jchen208208/SPARC-Spotify-Proximity-and-Remote-Control/core.py

# serial/Bluetooth handling, port discovery, Spotify client and actions, volume ramping, and run_worker

import os
import sys
import io
import queue
import shutil
import subprocess
import time
import threading
import requests
import serial
import serial.tools.list_ports
import json
import spotipy
import pygame
from spotipy.oauth2 import SpotifyOAuth
from dotenv import load_dotenv

# --- Windowed builds (pyinstaller --windowed) have no console. Depending on
# the exact PyInstaller version / --onefile-vs-onedir combo, that shows up
# two different ways: sys.stdout/sys.stderr come back as plain None, OR
# they're real-looking objects that raise OSError("Bad file descriptor")
# the moment anything is actually written to them (a known quirk of the
# --onefile --windowed bootloader on Windows). The old fix here only
# checked for the None case, so on this build it did nothing, and every
# print() call in this file (there are a lot - they're this app's only
# debugging output) would kill whatever thread hit it first. A background
# thread's uncaught exception ends that thread with no visible error, which
# is exactly what was happening: the windowed build would connect fine,
# then die silently on the very first "Controller connected on {port}."
# print - right before the line that starts the serial-reading thread - so
# gestures could never be read at all, while the UI kept showing "Connected"
# because that status had already been set a line earlier.
#
# Fix: test-write to both streams (catches either failure mode) and, if
# either is broken, swap in a stream that can never raise - backed by a log
# file rather than os.devnull, so hiding the console doesn't mean losing all
# visibility. This has to happen before pygame is imported below: pygame
# prints a "Hello from the pygame community" line the instant it's
# imported, and that would crash right here otherwise.


class _SafeLogStream:
    """A write target that can never raise, no matter what's wrong with the
    real stdout/stderr. Backed by a real file when possible so hiding the
    console doesn't mean losing all visibility into what the app is doing."""

    def __init__(self, path):
        try:
            self._f = open(path, "w", buffering=1, encoding="utf-8", errors="replace")
        except OSError:
            self._f = None  # e.g. nowhere writable - fall through to silence

    def write(self, data):
        if self._f is not None:
            try:
                self._f.write(data)
            except Exception:
                self._f = None  # proven broken - stop trying, just swallow from here on

    def flush(self):
        if self._f is not None:
            try:
                self._f.flush()
            except Exception:
                pass

    def isatty(self):
        return False


def _is_broken(stream):
    """True if writing to `stream` raises - covers both "it's None" and "it
    looks fine but dies on write" without needing to know which one a given
    PyInstaller build produces."""
    if stream is None:
        return True
    try:
        stream.write("")
        stream.flush()
        return False
    except Exception:
        return True


if _is_broken(sys.stdout) or _is_broken(sys.stderr):
    _log_dir = os.path.join(os.path.expanduser("~"), ".sparc_cache")
    try:
        os.makedirs(_log_dir, exist_ok=True)
    except OSError:
        pass
    _log = _SafeLogStream(os.path.join(_log_dir, "sparc.log"))
    sys.stdout = _log
    sys.stderr = _log

# --- Everything else, now that stdout/stderr are safe to write to ---


# --- Resolve base directory whether frozen (PyInstaller) or running as .py ---
if getattr(sys, 'frozen', False):
    BASE_DIR = sys._MEIPASS                    # bundled assets (fonts/images/sounds)
    ENV_DIR = os.path.dirname(sys.executable)  # .env stays external, next to the built exe
else:
    BASE_DIR = ENV_DIR = os.path.dirname(os.path.abspath(__file__))

load_dotenv(os.path.join(ENV_DIR, '.env'))

BAUD_RATE = 9600
HANDSHAKE_TIMEOUT = 4.0  # a port must answer within this to count as our board
SCOPE = ("user-modify-playback-state user-read-playback-state "
         "user-read-currently-playing user-read-recently-played")

VOLUME_STEP = 5
VOLUME_INTERVAL = 0.2
ESP32_OUI = "8C94DF"

# Windows-only: exact MAC suffixes for our paired boards. The bare OUI above
# matches any Espressif device in earshot, not just ours - add each board's
# last MAC byte(s) here (e.g. "68" matches "8C94DF68").
ESP32_MAC_SUFFIXES = {"68"}

pygame.mixer.init()

ASSET_DIR = os.path.join(BASE_DIR, "SPARC_assets")
SOUND_CONNECTED = os.path.join(ASSET_DIR, "connected.mp3")
SOUND_DISCONNECTED = os.path.join(ASSET_DIR, "disconnected.mp3")

# The Nano and the Uno both reach us through an HC-05 module; the ESP32 uses
# its own radio and advertises itself as "SPARC" (see sketch_esp). Past the
# open() all three speak the same line protocol, so the board only ever differs
# in which serial port it shows up as - hence one script for all three.
# Espressif's OUI - the first three bytes of every ESP32's Bluetooth MAC. Windows
# hides the device name but puts the MAC in the port's hwid, so this is what finds
# the board there. It identifies the *vendor*, not the board: if two ESP32s are
# paired, both match and the handshake picks whichever answers - set BT_PORT to
# pin one. (Boards from other Espressif batches have a different OUI and fall
# through to the Bluetooth-port sweep below, which finds them too, just slower.)

DEVICE_HINTS = ("SPARC", "HC-05", "HC05", "ESP32", ESP32_OUI)


def candidate_ports(verbose=False):
    """Serial ports that might be a SPARC controller, most likely first.

    The two OSes tell us completely different things about a Bluetooth port, so
    we match on whatever each one actually gives us:

    macOS names the port after the device (/dev/cu.SPARC, /dev/cu.HC-05), so the
    name hints match outright - but it never exposes a MAC (hwid is "n/a").

    Windows is the mirror image: the description is always "Standard Serial over
    Bluetooth link", with no trace of the device name, but the MAC *is* there in
    the hwid. So we match Espressif's OUI - the first three bytes of every ESP32's
    MAC - which is how the Windows side has always identified the board. Anything
    Bluetooth-ish that we can't identify is still offered up as a last resort, and
    open_device()'s handshake decides which one is really ours.
    """
    named, fallback, seen = [], [], []
    for port in serial.tools.list_ports.comports():
        blob = " ".join(filter(None, (port.device, port.description, port.hwid))).upper()
        seen.append(f"{port.device} | {port.description} | {port.hwid}")
        if sys.platform == "win32":
            # Windows never exposes the device name, only the MAC in hwid, and
            # the bare OUI matches any Espressif board, not just ours - require
            # an exact suffix match and ignore everything else on this OS.
            if any(f"{ESP32_OUI}{suffix}" in blob for suffix in ESP32_MAC_SUFFIXES):
                named.append(port.device)
            continue
        if any(hint in blob for hint in DEVICE_HINTS):
            named.append(port.device)
    if verbose and not named and not fallback:
        # Turn "it doesn't find the port" into something diagnosable rather than
        # a silent empty list - this is the only place that knows what the OS saw.
        print("No candidate ports. Serial ports visible to this machine:")
        for line in seen or ["  (none at all)"]:
            print(f"    {line}")
        print("  If the board is paired, add its port to .env as BT_PORT=<port>.")
    return named + fallback


PORT_CACHE = os.path.join(os.path.expanduser("~"), ".sparc_cache", "port.json")


def _load_cached_port():
    """The port that answered last time this machine ran. Probing a Bluetooth
    port that turns out to be dead costs ~4s, so on a machine with several
    boards paired a cold scan is slow; remembering the winner makes every run
    after the first go straight to it."""
    try:
        with open(PORT_CACHE) as f:
            return json.load(f).get("port")
    except (OSError, ValueError):
        return None


def _save_cached_port(port):
    try:
        os.makedirs(os.path.dirname(PORT_CACHE), exist_ok=True)
        with open(PORT_CACHE, "w") as f:
            json.dump({"port": port}, f)
    except OSError:
        pass


def resolve_ports(preferred=None):
    """Ports to try this round: last known good, then the .env override, then
    the port cached from a previous run, then whatever autodetect turns up.
    Re-run on every reconnect rather than once at startup, so a board powered on
    after the app is still picked up. A stale entry costs nothing: it just fails
    the handshake and we fall through to the next candidate."""
    ports = []
    for port in (preferred, os.getenv("BT_PORT"), _load_cached_port()):
        if port and port not in ports:
            ports.append(port)
    for port in candidate_ports(verbose=not ports):
        if port not in ports:
            ports.append(port)
    return ports


def open_device(port):
    """Open `port` and prove a real controller is on the other end, else None.
    A successful open() means nothing by itself: macOS hands back the port of a
    paired-but-powered-off HC-05 quite happily, and on Windows we may well be
    probing some unrelated Bluetooth device. Without this proof we'd flip to
    "connected", time out on the silence seconds later, reconnect, and loop
    forever spamming the connect/disconnect sounds. The probe is re-sent each
    tick so a still-booting board isn't rejected for missing the first one.
    The Nano and ESP32 answer "ACK" and the Uno answers "HB" - any line at all
    is proof of life, so we needn't care which board we got.
    """
    ser = serial.Serial(port, BAUD_RATE, timeout=0.3)
    try:
        ser.reset_input_buffer()
        deadline = time.time() + HANDSHAKE_TIMEOUT
        while time.time() < deadline:
            ser.write(b"HB\n")
            ser.flush()
            if ser.readline().decode("utf-8", errors="ignore").strip():
                return ser
    except (serial.SerialException, OSError):
        pass
    try:
        ser.close()  # don't leak a half-open port on every failed probe
    except Exception:
        pass
    return None


def _blueutil_path():
    """Locate blueutil even when PATH is minimal (e.g. a PyInstaller app
    launched from Finder, which doesn't inherit a shell's PATH)."""
    return (shutil.which("blueutil")
            or next((p for p in ("/opt/homebrew/bin/blueutil",
                                 "/usr/local/bin/blueutil")
                     if os.path.exists(p)), None))


def _resolve_bt_addr(port):
    """macOS: map the serial port back to its Bluetooth MAC so a stale link can
    be forced down on disconnect. macOS otherwise keeps the dropped RFCOMM
    channel half-open and refuses to re-establish it until the device is
    manually removed and re-paired. Honours a BT_MAC override in .env."""
    if sys.platform != "darwin" or not port:
        return None
    addr = os.getenv("BT_MAC")
    if addr:
        return addr
    blueutil = _blueutil_path()
    if not blueutil:
        return None
    name = os.path.basename(port).replace("cu.", "").replace("tty.", "")
    try:
        out = subprocess.run([blueutil, "--paired"], capture_output=True,
                             text=True, timeout=5).stdout
    except Exception:
        return None
    for line in out.splitlines():
        if f'name: "{name}"' in line:
            return line.split("address:")[1].split(",")[0].strip()
    return None


def force_bt_disconnect(port):
    """Tear down the OS-level Bluetooth link to the board. After an abrupt power
    loss macOS leaves the RFCOMM channel half-open, which blocks every reconnect
    attempt until it's dropped - this is the programmatic equivalent of 'forget
    & re-add' minus the unpairing, so the next port open() negotiates a fresh
    link. Best-effort and a no-op off macOS / without blueutil."""
    addr = _resolve_bt_addr(port)
    if not addr:
        return
    blueutil = _blueutil_path()
    if not blueutil:
        return
    try:
        subprocess.run([blueutil, "--disconnect", addr],
                       capture_output=True, timeout=5)
    except Exception:
        pass


def play_sound(path):
    try:
        pygame.mixer.music.load(path)
        pygame.mixer.music.play()
    except Exception as e:
        print(f"  Sound error: {e}")


def get_spotify():
    cache_dir = os.path.join(os.path.expanduser("~"), ".sparc_cache")
    os.makedirs(cache_dir, exist_ok=True)
    cache_path = os.path.join(cache_dir, ".spotify_cache")
    auth = SpotifyOAuth(
        client_id=os.getenv("SPOTIPY_CLIENT_ID"),
        client_secret=os.getenv("SPOTIPY_CLIENT_SECRET"),
        redirect_uri=os.getenv("SPOTIPY_REDIRECT_URI"),
        scope=SCOPE,
        open_browser=True,
        cache_path=cache_path,
    )
    return spotipy.Spotify(auth_manager=auth)


_art_cache = {}
_art_cache_lock = threading.Lock()


def fetch_album_art(url):
    """Download and cache album art by URL (Spotify's smallest size, ~64x64).
    Returns a pygame Surface, or None on any failure so callers can fall back
    to a placeholder. Scaling to display size happens at draw time, since
    prev/current/next render the same image at different sizes."""
    if not url:
        return None
    with _art_cache_lock:
        if url in _art_cache:
            return _art_cache[url]
    try:
        # requests (not urllib) so certifi's CA bundle is used - macOS
        # python.org builds have no system certs and fail SSL verification.
        resp = requests.get(url, timeout=4)
        resp.raise_for_status()
        surf = pygame.image.load(io.BytesIO(resp.content))
    except Exception as e:
        print(f"  Album art error: {e}")
        surf = None
    with _art_cache_lock:
        _art_cache[url] = surf
    return surf


_ser_write_lock = threading.Lock()


def ser_write(ser, data):
    """Best-effort thread-safe write to the shared serial connection.
    Several threads (heartbeat, volume ramp, command handlers) can write
    to the Arduino concurrently - the lock keeps their messages from
    interleaving mid-line, and a bad/closed port is just silently skipped
    the same way every call site already treated it."""
    if not ser or not ser.is_open:
        return
    try:
        with _ser_write_lock:
            ser.write(data)
            ser.flush()
    except Exception:
        pass


def send_current_volume(sp, ser):
    try:
        playback = sp.current_playback()
        if playback and playback.get("device"):
            vol = playback["device"].get("volume_percent", 0)
            ser_write(ser, f"VOL{vol}\n".encode())
    except Exception:
        pass


# --- Volume ramping (background thread) ---

_volume_stop = threading.Event()
_volume_thread = None
_volume_lock = threading.Lock()


def _ramp_volume(sp, direction, ser):
    _volume_stop.clear()
    try:
        playback = sp.current_playback()
        if not playback or not playback.get("device"):
            return
        device = playback["device"]
        current = device.get("volume_percent", 50)
        device_id = device["id"]
    except Exception as e:
        print(f"  Volume error: {e}")
        return

    if (direction == 1 and current >= 100) or (direction == -1 and current <= 0):
        _volume_stop.set()
        ser_write(ser, b"VS\n")
        print(f"  Already at {'max' if direction == 1 else 'min'} volume")
        return

    while not _volume_stop.wait(VOLUME_INTERVAL):
        try:
            current = max(0, min(100, current + direction * VOLUME_STEP))
            sp.volume(int(current), device_id=device_id)
            print(f"  Volume: {current}%")
            ser_write(ser, f"VOL{int(current)}\n".encode())
            if current in (0, 100):
                _volume_stop.set()
                ser_write(ser, b"VS\n")
                break
        except Exception as e:
            print(f"  Volume error: {e}")
            break


def start_volume(sp, direction, ser):
    global _volume_thread
    note_action("volup" if direction > 0 else "voldown")
    with _volume_lock:
        _volume_stop.set()
        if _volume_thread is not None and _volume_thread.is_alive():
            _volume_thread.join(timeout=0.5)
        _volume_thread = threading.Thread(target=_ramp_volume, args=(sp, direction, ser), daemon=True)
        _volume_thread.start()


def stop_volume():
    _volume_stop.set()


def volume_active():
    if _volume_thread is None:
        return False
    return _volume_thread.is_alive()


# --- Spotify actions ---

LAST_ACTION = {"name": None, "time": 0.0}


def note_action(name):
    LAST_ACTION["name"] = name
    LAST_ACTION["time"] = time.time()


def next_track(sp, ser):
    sp.next_track()
    note_action("next")
    print("  Next track")
    time.sleep(0.3)
    send_current_volume(sp, ser)


def prev_track(sp, ser):
    try:
        playback = sp.current_playback()
        if not playback:
            return
        position = playback.get("progress_ms", 0)
        if position > 3000:
            sp.seek_track(0)
            note_action("restart")
            print("  ↩ Restarted track")
        else:
            sp.previous_track()
            note_action("prev")
            print("  ⏮ Previous track")
    except spotipy.exceptions.SpotifyException as e:
        if "403" in str(e):
            print("  Previous track unavailable")
        else:
            raise
    time.sleep(0.3)
    send_current_volume(sp, ser)


def toggle_pause(sp, ser):
    playback = sp.current_playback()
    if playback and playback.get("is_playing"):
        sp.pause_playback()
        note_action("pause")
        print("  Paused")
    else:
        devices = sp.devices().get("devices", [])
        device_id = devices[0]["id"] if devices else None
        sp.start_playback(device_id=device_id)
        note_action("play")
        print("  Resumed")
    time.sleep(0.3)
    send_current_volume(sp, ser)


def handle_stop(sp, ser):
    if volume_active():
        stop_volume()
        if _volume_thread is not None:
            _volume_thread.join(timeout=0.5)
        ser_write(ser, b"VS\n")
        print("  Volume stopped")
    else:
        toggle_pause(sp, ser)


def get_handlers(ser):
    return {
        "S+": lambda sp: next_track(sp, ser),
        "S-": lambda sp: prev_track(sp, ser),
        "V+": lambda sp: start_volume(sp, +1, ser),
        "V-": lambda sp: start_volume(sp, -1, ser),
        "P": lambda sp: handle_stop(sp, ser),
    }


def _serial_reader(ser, line_queue, stop_flag):
    """Runs in its own thread and does nothing but pull lines off the wire.

    If the HC-05 loses power, the underlying OS Bluetooth stack can leave
    a blocking read() hanging well past pyserial's own `timeout` setting -
    often 20-30s - while it waits out its own link-supervision timeout
    before reporting the port as dead. Isolating the read here means that
    hang never stops the main loop from independently noticing (on its own
    clock, via the queue below) that no data has arrived in a while and
    reacting immediately, instead of being stuck waiting for this call to
    return.
    """
    while not stop_flag.is_set():
        try:
            raw = ser.readline()
        except Exception:
            line_queue.put(None)  # sentinel: the port has died
            return
        if not raw:
            continue
        line = raw.decode("utf-8", errors="ignore").strip()
        if line:
            line_queue.put(line)


def _dispatch_command(handler, sp, line):
    """Runs a Spotify command handler on its own thread, so a slow Spotify
    API call can never block the main loop's disconnect-detection timing -
    that coupling was what caused occasional timeouts unrelated to the
    Arduino actually going away."""
    try:
        handler(sp)
    except spotipy.exceptions.SpotifyException as e:
        print(f"  Spotify error: {e}")
    except Exception as e:
        print(f"  Error: {e}")


def run_worker(stop_event, status):

    sp = get_spotify()

    print("Connecting to Spotify...")
    try:
        user = sp.current_user()
        user_name = user["display_name"]
        status["spotify"] = "Checking Spotify device..."
        status["spotify_state"] = "wait"
        print(f"Logged in as: {user_name}\n")
    except Exception as e:
        status["spotify"] = "Login failed"
        status["spotify_state"] = "err"
        print(f"Spotify auth failed: {e}")
        return

    ser = None
    active_port = None  # last port that actually handshook - retried first
    arduino_connected = False
    spotify_connected = False
    spotify_fail_count = 0  # consecutive failed Spotify polls; see update_spotify_status
    was_connected = False
    HANDLERS = {}
    line_queue = queue.Queue()
    reader_stop = threading.Event()
    last_heartbeat = 0.0
    last_rx_time = time.time()
    last_spotify_check = 0.0
    # Command handlers now run on their own thread (see _dispatch_command),
    # so a slow Spotify call can no longer stall this loop - ARDUINO_TIMEOUT
    # only has to cover real silence from the Arduino itself.
    ARDUINO_TIMEOUT = 3.0
    HEARTBEAT_INTERVAL = 1.0
    SPOTIFY_CHECK_INTERVAL = 5.0
    SPOTIFY_FAIL_THRESHOLD = 2  # consecutive failed polls (~10s) before we call it disconnected
    track_state = {"prev": None, "current_id": None}

    def close_arduino_link(state):
        nonlocal ser, arduino_connected, was_connected
        print("Disconnected.")
        status["arduino"] = "Arduino disconnected"
        status["arduino_state"] = state
        arduino_connected = False
        if was_connected:
            play_sound(SOUND_DISCONNECTED)
            was_connected = False
            ser_write(ser, b"VOL0\n")
        reader_stop.set()
        try:
            ser.close()
        except Exception:
            pass
        ser = None
        # Force macOS to drop the (now half-open) Bluetooth channel so the
        # reconnect loop below can negotiate a fresh link when the board comes
        # back - without this, reopening the port silently reuses the stale
        # channel and never reconnects.
        force_bt_disconnect(active_port)

    def _track_info(item):
        # images are ordered largest first; take the middle (~300px) size -
        # the UI now shows the cover big, so the 64px one looks mushy.
        images = item.get("album", {}).get("images", [])
        art_url = images[1]["url"] if len(images) > 1 else (images[0]["url"] if images else None)
        return {
            "id": item.get("id"),
            "name": item.get("name", ""),
            "artist": ", ".join(a["name"] for a in item.get("artists", [])),
            "art": fetch_album_art(art_url),
        }

    def _update_track_state(item, context_uri):
        # Spotify's API has no "previous track" endpoint, so prev is inferred
        # by watching the current track ID change between polls. A skip that
        # happens between two polls (SPOTIFY_CHECK_INTERVAL apart) can be
        # missed if two changes land in the same window.
        # All slow work (art downloads, the order/queue round-trips) happens
        # before any status key is written, so the UI never sees a
        # half-updated snapshot - e.g. the new current track next to the old
        # queue.
        info = _track_info(item)
        window = _playlist_window(context_uri, item.get("id"))
        if window is not None:
            # The context's running order is known: both sides of the wheel
            # come straight from it, and the queue round-trip is skipped.
            prevs, qinfos = window
        else:
            prevs = None
            try:
                q_items = sp.queue().get("queue", [])
                qinfos = [_track_info(q) for q in q_items[:5]]
            except Exception:
                qinfos = []
        cur_id = item.get("id")
        if cur_id and cur_id != track_state["current_id"]:
            if track_state["current_id"] is not None:
                track_state["prev"] = status.get("track_current")
            track_state["current_id"] = cur_id
        status["track_prev"] = track_state["prev"]
        status["track_prevs"] = prevs
        status["track_queue"] = qinfos
        status["track_current"] = info

    def update_spotify_status():
        nonlocal spotify_connected, spotify_fail_count
        playing = False
        try:
            playback = sp.current_playback()
            if playback and playback.get("device"):
                spotify_connected = True
                spotify_fail_count = 0
                playing = bool(playback.get("is_playing"))
                context = playback.get("context")
                # Context lands before the track: on a playlist switch the
                # UI hard-cuts when the URI changes, so the new track then
                # reads as a clean cold start instead of animating across
                # contexts.
                status["context_uri"] = context.get("uri") if context else None
                status["shuffle"] = bool(playback.get("shuffle_state"))
                item = playback.get("item")
                if item:
                    _update_track_state(item, status["context_uri"])
            else:
                devices = sp.devices().get("devices", [])
                spotify_connected = bool(devices)
                if spotify_connected:
                    spotify_fail_count = 0
        except Exception as e:
            # A single failed poll is usually a network blip or a Spotify
            # rate limit, not a real disconnect - only give up on the
            # connection after a few in a row (mirrors ARDUINO_TIMEOUT's
            # grace period on the serial side). Logged so a persistent drop
            # shows its real cause here instead of just going silent.
            spotify_fail_count += 1
            print(f"  Spotify poll failed ({spotify_fail_count}/{SPOTIFY_FAIL_THRESHOLD}): {e}")
            if spotify_fail_count >= SPOTIFY_FAIL_THRESHOLD:
                spotify_connected = False
        status["playing"] = playing
        if spotify_connected:
            status["spotify"] = f"Logged in as {user_name}"
            status["spotify_state"] = "ok"
        else:
            status["spotify"] = "No active Spotify device"
            status["spotify_state"] = "err"

    # One context's full running order, fetched once and reused every poll.
    # The Web API never says where the playing track sits in its context -
    # current_playback() gives the track and the context URI, nothing more -
    # so the order is fetched wholesale and the position found by ID.
    # "missing" remembers an ID that wasn't in the list (a one-off queued
    # track, a playlist past the fetch cap) so it isn't refetched every poll.
    ctx_order = {"uri": None, "items": None, "ids": [], "missing": None}

    def _fetch_context_items(uri):
        # Playlists and albums are the contexts with a readable running
        # order; radio, liked songs and bare tracks aren't pageable, and
        # very deep playlists get cut off rather than paged forever.
        kind = uri.split(":")[1] if uri.count(":") >= 2 else None
        if kind == "album":
            alb = sp.album(uri)
            items = alb.get("tracks", {}).get("items", [])
            for tr in items:
                tr["album"] = alb  # album tracks omit it, and art lives there
            return items
        if kind != "playlist":
            return None
        fields = "items(track(id,name,artists(name),album(images))),next"
        items, offset = [], 0
        while offset < 500:
            page = sp.playlist_items(uri, fields=fields, limit=100, offset=offset)
            items.extend(it.get("track") for it in page.get("items", []) if it.get("track"))
            if not page.get("next"):
                break
            offset += 100
        return items

    def _refresh_ctx_order(uri):
        items = _fetch_context_items(uri)
        ctx_order.update(uri=uri, items=items, missing=None,
                         ids=[tr.get("id") for tr in (items or [])])

    def _playlist_window(uri, cur_id):
        # (prevs, nexts) around the current track in *playlist* order, or
        # None when the order can't be known. Shuffle deliberately doesn't
        # change this: the wheel shows the playlist as written, not the play
        # order - a shuffled skip just recenters the window (the UI's "jump"
        # crossfade) instead of spinning one seat over.
        if not uri or not cur_id:
            return None
        try:
            if ctx_order["uri"] != uri:
                _refresh_ctx_order(uri)
            elif (ctx_order["items"] is not None and cur_id != ctx_order["missing"]
                    and cur_id not in ctx_order["ids"]):
                # Not there? The playlist may have been edited since the
                # fetch - look again, once per unknown ID.
                _refresh_ctx_order(uri)
        except Exception as e:
            print(f"  Context order unavailable: {e}")
            ctx_order["uri"] = None  # retry from scratch next poll
            return None
        if ctx_order["items"] is None:
            return None
        if cur_id not in ctx_order["ids"]:
            ctx_order["missing"] = cur_id  # e.g. a queued one-off track
            return None
        # A track that appears twice in one playlist is ambiguous - the API
        # doesn't say which copy is playing - so the first occurrence wins.
        i = ctx_order["ids"].index(cur_id)
        items = ctx_order["items"]
        return ([_track_info(tr) for tr in items[max(0, i - 5):i]],
                [_track_info(tr) for tr in items[i + 1:i + 6]])

    def _recently_played():
        # Spotify's recently-played endpoint knows what came before this
        # session, so the wheel's prev slots get real covers from the first
        # frame instead of waiting for tracks to change while the app runs.
        try:
            items = sp.current_user_recently_played(limit=12).get("items", [])
        except Exception as e:
            print(f"  Recently played unavailable: {e}")
            return []
        # Tracks skipped past earlier show up both here and in the upcoming
        # queue; seeding those would put the same cover on both sides of the
        # wheel, so anything queued is excluded from history.
        skip = {track_state["current_id"]}
        skip.update(tr["id"] for tr in status.get("track_queue") or []
                    if tr and tr.get("id"))
        hist, last_id = [], None
        for it in items:  # newest first
            tr = it.get("track")
            if not tr or not tr.get("id") or tr["id"] in skip or tr["id"] == last_id:
                continue
            hist.append(_track_info(tr))
            last_id = tr["id"]
            if len(hist) == 5:
                break
        return hist[::-1]  # oldest first, like the UI's hist

    def seed_history():
        # One-shot fallback seed for contexts whose running order can't be
        # read (radio, liked songs). When the order IS readable, track_prevs
        # (kept live above) fills the left of the wheel continuously and no
        # seed is wanted.
        if status.get("track_prevs") is not None:
            status["track_history"] = []
        else:
            status["track_history"] = _recently_played()

    update_spotify_status()
    seed_history()
    last_spotify_check = time.time()

    while not stop_event.is_set():
        # --- Bluetooth reconnect FIRST ---
        # This runs before the Spotify check so plugging the Arduino back in
        # is picked up on the very next loop tick instead of waiting behind a
        # (potentially slow) Spotify API round trip. No `continue` on failure
        # here - that's what let the disconnect-sound check get skipped
        # before; instead we just fall through to the state evaluation below
        # every time, connected or not.
        if ser is None or not ser.is_open:
            arduino_connected = False
            ports = resolve_ports(active_port)
            if not ports:
                status["arduino"] = "No controller found"
                status["arduino_state"] = "wait"
            # Probe each candidate in turn: whichever one answers the handshake
            # is the board, be it a Nano, an Uno or an ESP32. Windows can't tell
            # us the device name of a Bluetooth port, so this is what stands in
            # for recognising it by name there.
            for port in ports:
                if stop_event.is_set():
                    break
                status["arduino"] = f"Waiting for controller on {port}..."
                status["arduino_state"] = "wait"
                print(f"Waiting for controller on {port}...")
                try:
                    ser = open_device(port)
                except (serial.SerialException, OSError):
                    ser = None
                if ser:
                    active_port = port
                    _save_cached_port(port)
                    break

            if ser:
                HANDLERS = get_handlers(ser)
                arduino_connected = True
                last_rx_time = time.time()
                last_heartbeat = 0.0
                status["arduino"] = f"Connected on {active_port}"
                status["arduino_state"] = "ok"
                print(f"Controller connected on {active_port}.")
                # Force the Spotify check below to fire immediately, so
                # "both connected" is reflected right away instead of
                # waiting up to SPOTIFY_CHECK_INTERVAL seconds.
                last_spotify_check = 0.0
                # Fresh queue + reader thread for this connection. The old
                # reader thread (if any) is left to exit on its own; it holds
                # its own references and won't touch this new queue.
                line_queue = queue.Queue()
                reader_stop = threading.Event()
                threading.Thread(target=_serial_reader, args=(ser, line_queue, reader_stop), daemon=True).start()

        # --- Periodic Spotify check (independent of serial activity) ---
        # Also re-poll shortly after a control gesture (next/prev/...), so the
        # UI's cover-wheel animation fires right away instead of waiting out
        # the interval. The 0.4s settle gives Spotify's API time to reflect it.
        now = time.time()
        acted = LAST_ACTION["time"]
        if (now - last_spotify_check >= SPOTIFY_CHECK_INTERVAL
                or (acted > last_spotify_check and now - acted >= 0.4)):
            update_spotify_status()
            last_spotify_check = now

        # --- Evaluate combined state ---
        # Always runs (nothing above skips past it), so a disconnect is
        # never missed even while reconnect attempts keep failing.
        both_connected = arduino_connected and spotify_connected
        if both_connected and not was_connected:
            print("Connected.")
            play_sound(SOUND_CONNECTED)
            send_current_volume(sp, ser)
            was_connected = True
        elif not both_connected and was_connected:
            print("Disconnected.")
            play_sound(SOUND_DISCONNECTED)
            was_connected = False
            ser_write(ser, b"VOL0\n")

        if not arduino_connected:
            if stop_event.wait(0.5):
                break
            continue

        # --- Main loop: drain lines from the reader thread ---
        # Polling the queue (rather than calling ser.readline() here
        # directly) means this loop's timing is never at the mercy of a
        # blocking read - the timeout check below runs on schedule every
        # ~0.2s no matter how long the reader thread's read() call happens
        # to be stuck for.
        try:
            line = line_queue.get(timeout=0.2)
        except queue.Empty:
            line = ""

        if line is None:
            # Reader thread hit a hard serial error - the link is gone.
            close_arduino_link("wait")
            continue

        if not line:
            # No data right now - check whether the Arduino has gone quiet
            # for too long, or send a heartbeat to check that it's alive.
            if time.time() - last_rx_time > ARDUINO_TIMEOUT:
                close_arduino_link("wait")
                continue
            now = time.time()
            if now - last_heartbeat >= HEARTBEAT_INTERVAL:
                ser_write(ser, b"HB\n")
                last_heartbeat = now
            continue

        # Heartbeat reply — update rx time, skip print. The Nano and ESP32
        # sketches answer "ACK", the Uno sketch echoes "HB"; both mean alive.
        if line in ("ACK", "HB"):
            last_rx_time = time.time()
            continue

        last_rx_time = time.time()
        print(f"← {line}")
        handler = HANDLERS.get(line)
        if handler:
            # Dispatched on its own thread - a slow Spotify call here must
            # never delay the next iteration of this loop.
            threading.Thread(target=_dispatch_command, args=(handler, sp, line), daemon=True).start()
        else:
            print(f"  [unrecognized] {repr(line)}")

    # --- Cleanup on quit ---
    stop_volume()
    reader_stop.set()
    ser_write(ser, b"VOL0\n")
    if ser and ser.is_open:
        try:
            ser.close()
        except Exception:
            pass
    # Closing the port is not enough: macOS keeps the RFCOMM channel half-open
    # after we let go of it, and the next run silently reopens that dead channel
    # instead of negotiating a fresh one - which is what forces a manual "forget
    # this device & re-pair" between runs. Drop the link on the way out.
    force_bt_disconnect(active_port)
